bbenchoff/Raspi-BeBox/OtherGraphics/AOL.png

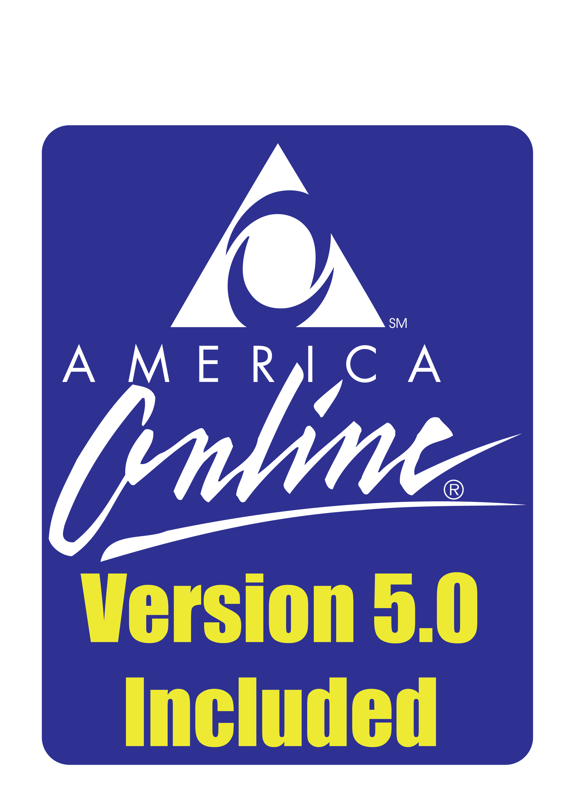
OtherGraphics/AOL.png
