bbenchoff/Raspi-BeBox/OtherGraphics/BigSticker.png

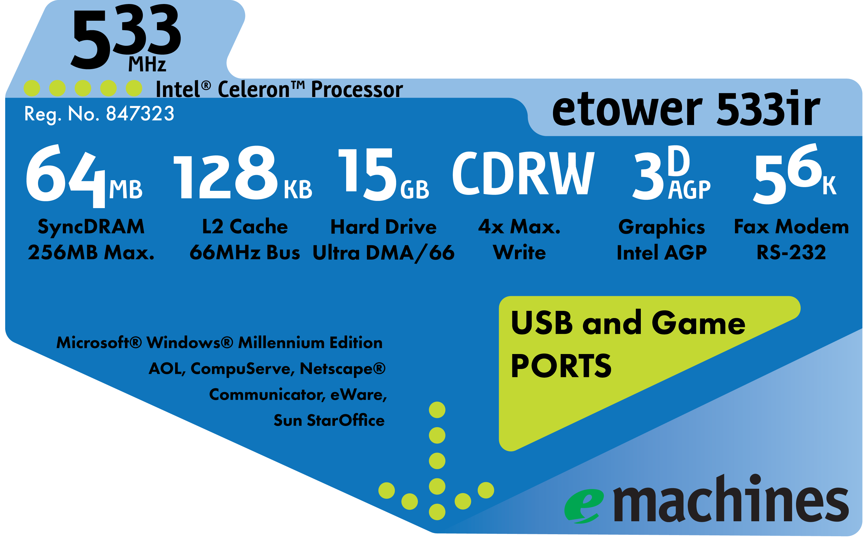
OtherGraphics/BigSticker.png
