bbenchoff/Raspi-BeBox/OtherGraphics/CDrw.png

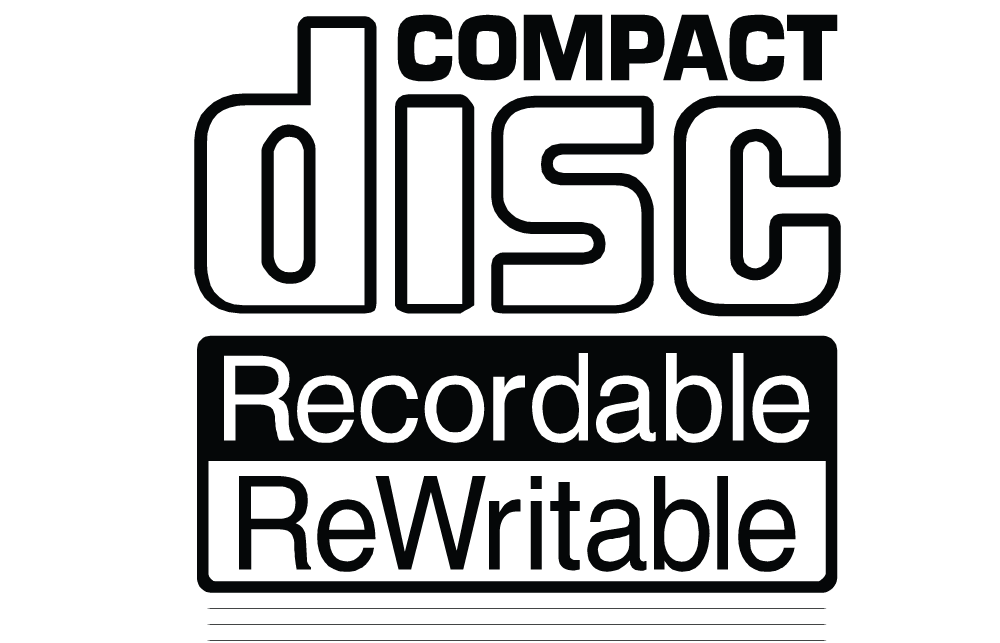
OtherGraphics/CDrw.png
