bbenchoff/Raspi-BeBox/OtherGraphics/Pentium.png

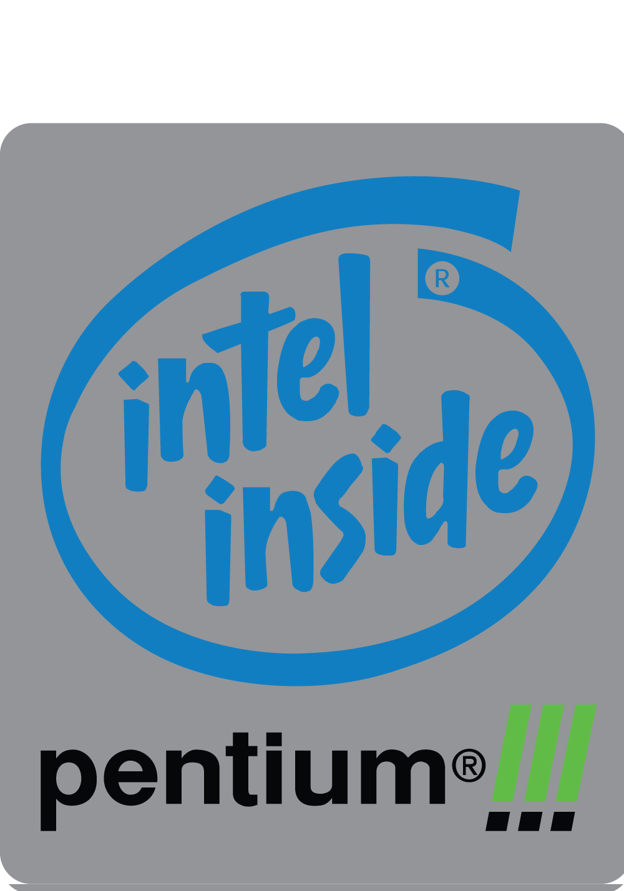
OtherGraphics/Pentium.png
