bbenchoff/Raspi-BeBox/OtherGraphics/Pentium_flipped.png

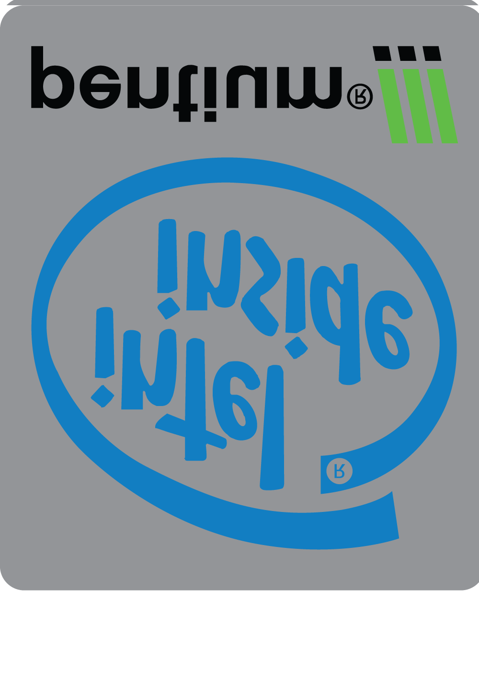
OtherGraphics/Pentium_flipped.png
