bbenchoff/Raspi-BeBox/OtherGraphics/Windows.png

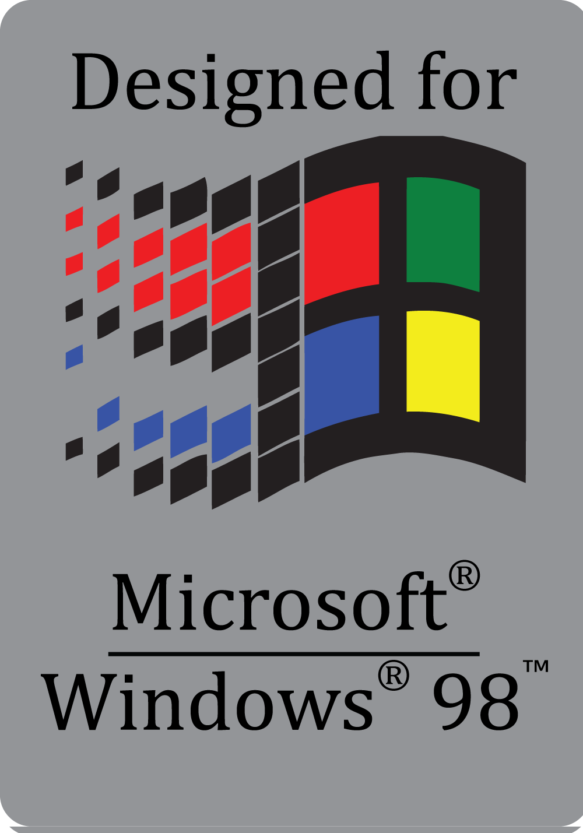
OtherGraphics/Windows.png
