bbenchoff/Raspi-BeBox/OtherGraphics/Windows_flipped.png

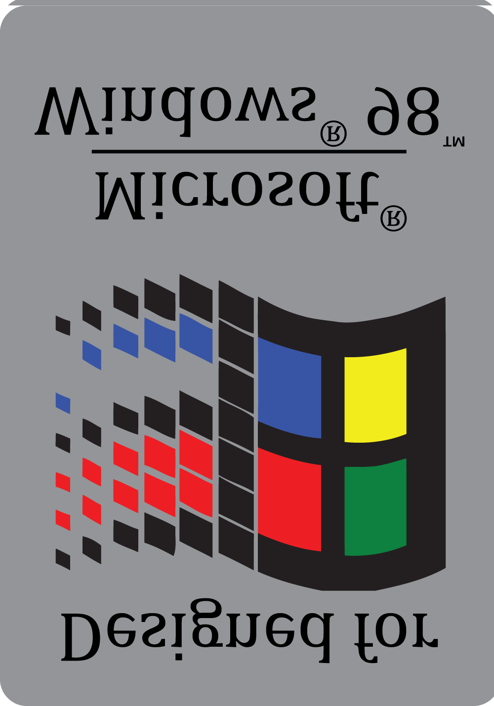
OtherGraphics/Windows_flipped.png
