bbenchoff/Raspi-BeBox/OtherGraphics/y2k.png

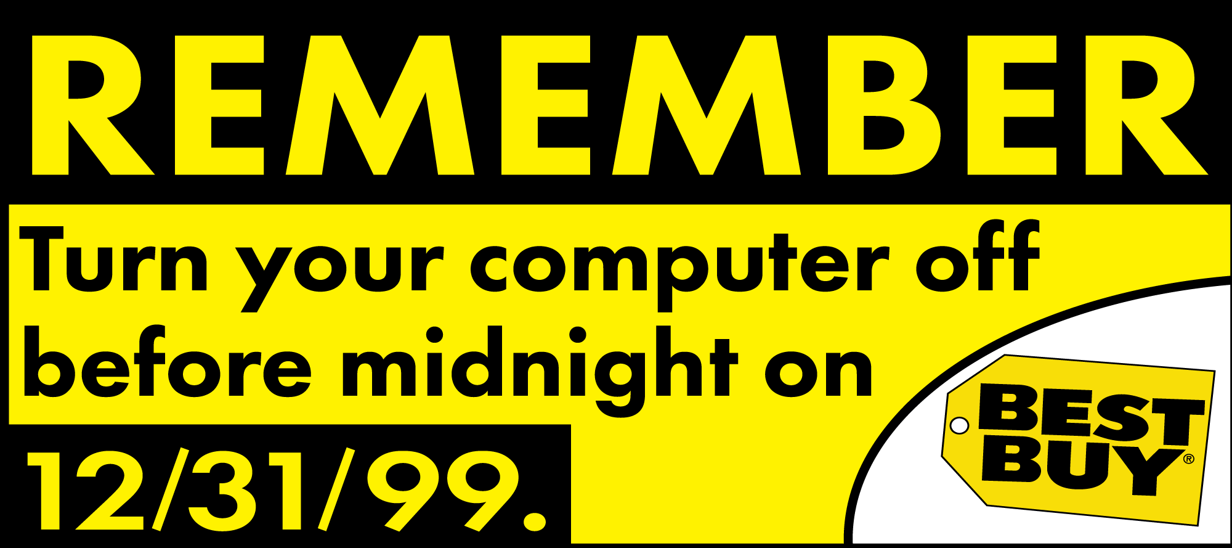
OtherGraphics/y2k.png
